dieseltravis/travis-ergogen-2024/key/output/pcbs/travis_key.kicad_pcb

## KiCad design key/output/pcbs/travis_key.kicad_pcb (2024-03-25)

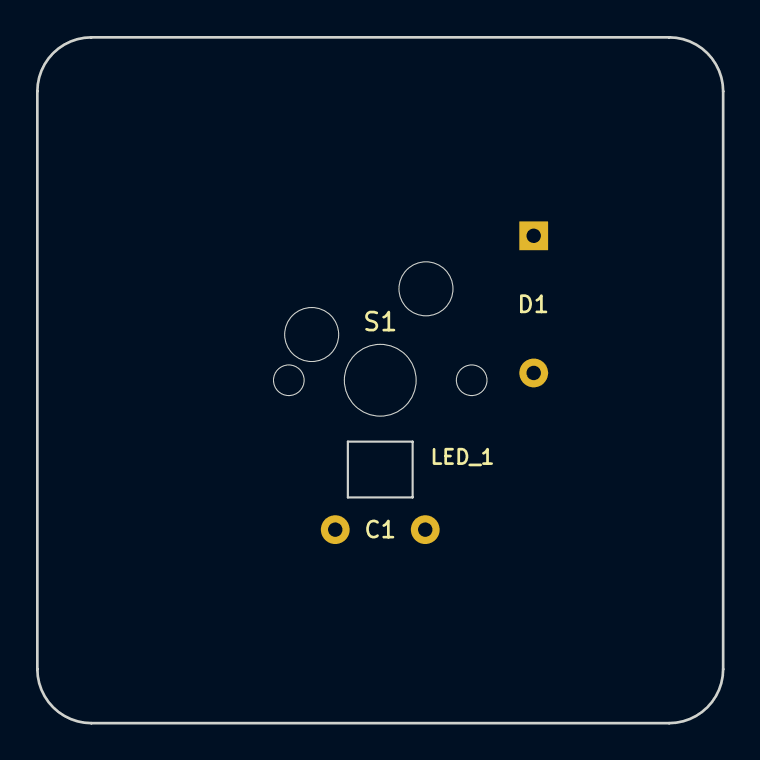
[picture p30: board travis_key.kicad_pcb from above]

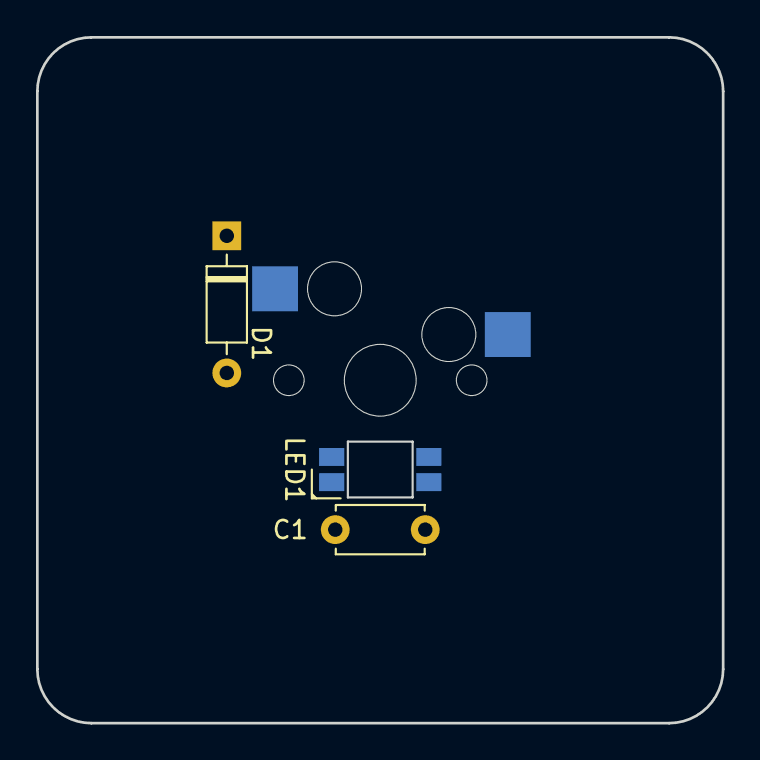
[picture p31: board travis_key.kicad_pcb from below]

Board: 2 copper layers, 38.1 x 38.1 mm, 4 parts (3 on the bottom side), 3 nets, no tracks yet.

Parts:
C1: 104; C_Disc_D4.7mm_W2.5mm_P5.00mm
D1: 1N4148; Diode_DO-35
LED1: SK6812mini-e; led_SK6812mini-e (per-key, single-side)
S1: Kailh MX Switch Sockets; MX

Connections:
GND: C1.2, LED1.3
RAW: C1.1, LED1.1
single_A_one: D1.2, S1.2
