dieseltravis/travis-ergogen-2024/keytest/output/pcbs/travis_keytest2.kicad_pcb

## KiCad design keytest/output/pcbs/travis_keytest2.kicad_pcb (2024-03-23)

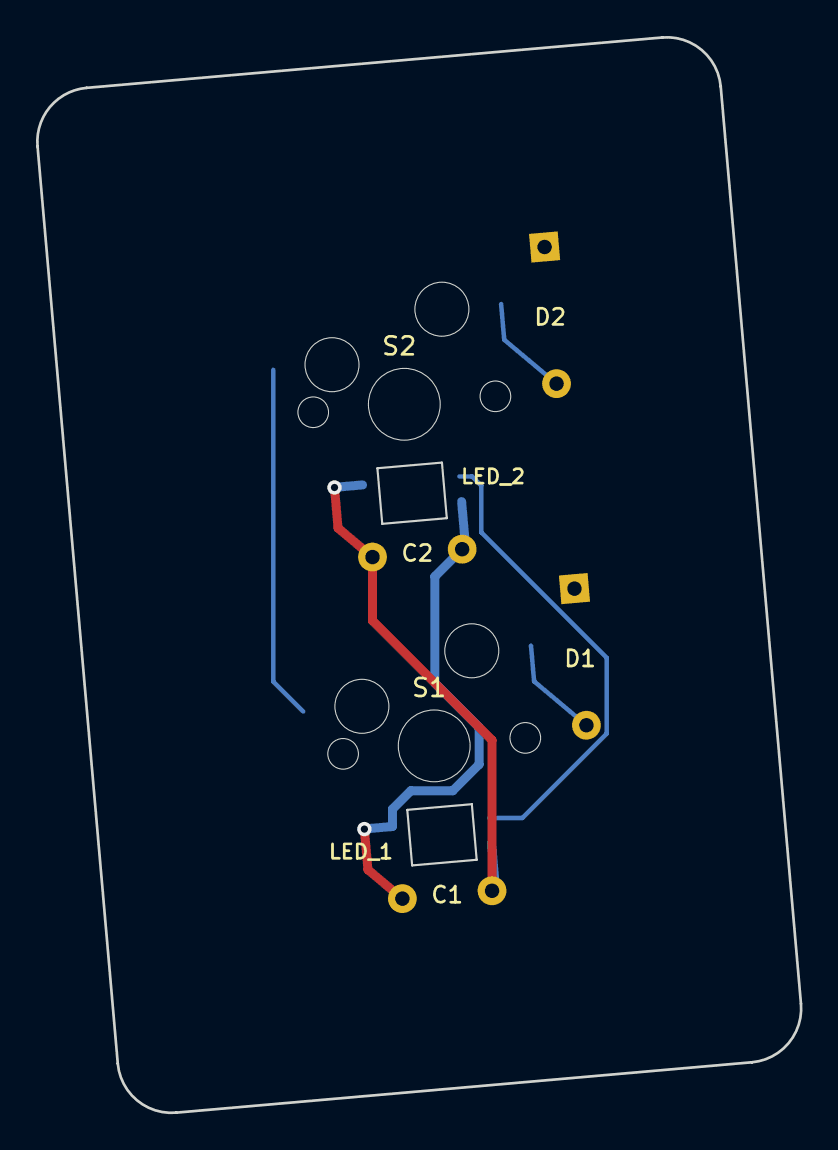
[picture p32: board travis_keytest2.kicad_pcb from above]

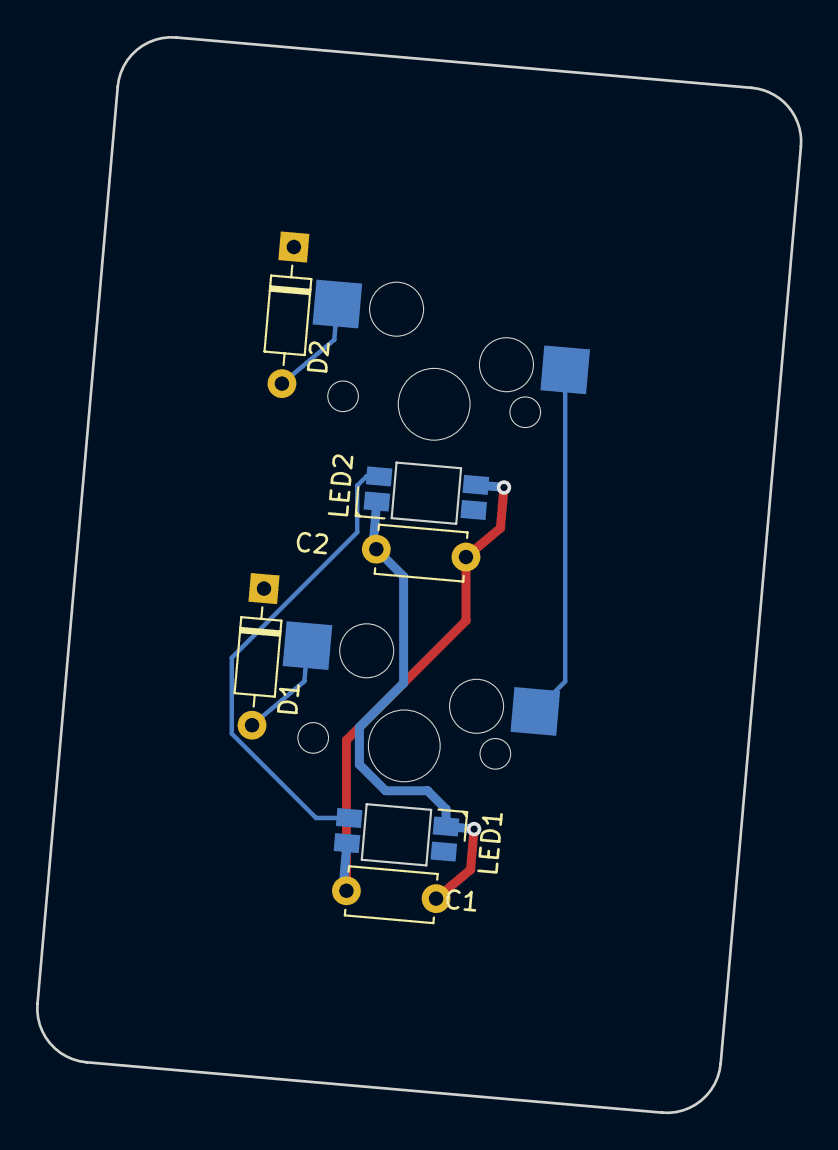
[picture p33: board travis_keytest2.kicad_pcb from below]

Board: 2 copper layers, 42.4 x 59.7 mm, 8 parts (6 on the bottom side), 6 nets.

Parts:
C1, C2: 104; C_Disc_D4.7mm_W2.5mm_P5.00mm
D1, D2: 1N4148; Diode_DO-35
LED1, LED2: SK6812mini-e; led_SK6812mini-e (per-key single-side)
S1, S2: Kailh MX Switch Sockets; MX

Connections:
GND: C1.2, C2.2, LED1.3, LED2.3
LED_2: LED1.2, LED2.4
RAW: C1.1, C2.1, LED1.1, LED2.1
col0: S1.1, S2.1
single_A_one: D1.2, S1.2
single_A_two: D2.2, S2.2
