dieseltravis/travis-ergogen-2024/output/pcbs/tutorial.kicad_pcb

## KiCad design output/pcbs/tutorial.kicad_pcb (2024-03-05)

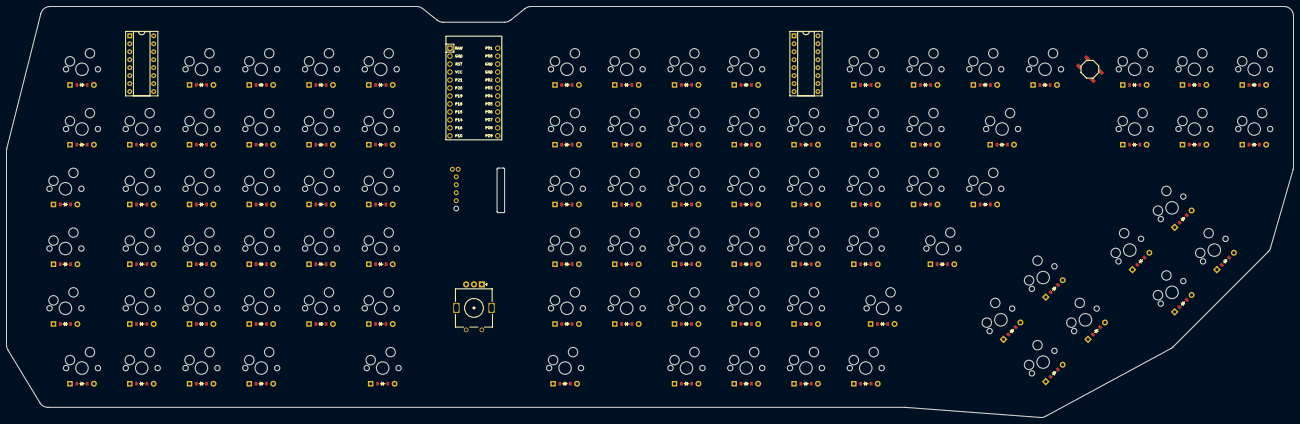
[picture p34: board tutorial.kicad_pcb from above]

Board: 2 copper layers, 410.2 x 131.0 mm, 185 parts (0 on the bottom side), 52 nets, no tracks yet.

Parts:
B1: SW_TACT_ALPS_SKQGABE010
D1, D2, D3, D4, D5, D6, D7, D8, D9, D10, D11, D12, D13, D14, D15, D16, D17, D18, D19, D20, D21, D22, D23, D24, D25, D26, D27, D28, D29, D30, D31, D32, D33, D34, D35, D36, D37, D38, D39, D40, D41, D42, D43, D44, D45, D46, D47, D48, D49, D50, D51, D52, D53, D54, D55, D56, D57, D58, D59, D60, D61, D62, D63, D64, D65, D66, D67, D68, D69, D70, D71, D72, D73, D74, D75, D76, D77, D78, D79, D80, D81, D82, D83, D84, D85, D86, D87, D88, D89, D90: ComboDiode
DIP1, DIP2: DIP-16_W7.62mm_Socket
MCU1: ProMicro
ROT1: rotary_encoder
S1, S2, S3, S4, S5, S6, S7, S8, S9, S10, S11, S12, S13, S14, S15, S16, S17, S18, S19, S20, S21, S22, S23, S24, S25, S26, S27, S28, S29, S30, S31, S32, S33, S34, S35, S36, S37, S38, S39, S40, S41, S42, S43, S44, S45, S46, S47, S48, S49, S50, S51, S52, S53, S54, S55, S56, S57, S58, S59, S60, S61, S62, S63, S64, S65, S66, S67, S68, S69, S70, S71, S72, S73, S74, S75, S76, S77, S78, S79, S80, S81, S82, S83, S84, S85, S86, S87, S88, S89, S90: MX

Connections:
GND: B1.1, DIP1.1, DIP1.2, DIP1.3, DIP1.4, DIP1.5, DIP1.6, DIP1.7, DIP1.8, DIP1.9, DIP1.10, DIP1.11, DIP1.12, DIP1.13, DIP1.14, DIP1.15, DIP2.1, DIP2.2, DIP2.3, DIP2.4, DIP2.5, DIP2.6, DIP2.7, DIP2.8, DIP2.9, DIP2.10, DIP2.11, DIP2.12, DIP2.13, DIP2.14, DIP2.15, MCU1.2, MCU1.15, MCU1.16, ROT1.1, ROT1.2, ROT1.A, ROT1.B, ROT1.C
RST: B1.2, MCU1.3
VCC: DIP1.16, DIP2.16, MCU1.4
index_bottom: D25.2, D41.2, S25.2, S41.2
index_func: D29.2, D45.2, S29.2, S45.2
index_home: D26.2, D42.2, S26.2, S42.2
index_mod: D24.2, S24.2
index_num: D28.2, D44.2, S28.2, S44.2
index_top: D27.2, D43.2, S27.2, S43.2
inner_bottom: D30.2, D36.2, S30.2, S36.2
inner_func: D34.2, D40.2, S34.2, S40.2
inner_home: D31.2, D37.2, S31.2, S37.2
inner_mod: D35.2, S35.2
inner_num: D33.2, D39.2, S33.2, S39.2
inner_top: D32.2, D38.2, S32.2, S38.2
left_bottom: D77.2, D81.2, D85.2, S77.2, S81.2, S85.2
left_top: D78.2, D82.2, D86.2, S78.2, S82.2, S86.2
mid_bottom: D87.2, S87.2
mid_top: D88.2, S88.2
middle_bottom: D19.2, D47.2, S19.2, S47.2
middle_func: D23.2, D51.2, S23.2, S51.2
middle_home: D20.2, D48.2, S20.2, S48.2
middle_mod: D18.2, D46.2, S18.2, S46.2
middle_num: D22.2, D50.2, S22.2, S50.2
middle_top: D21.2, D49.2, S21.2, S49.2
outer2_func: D72.2, S72.2
outer2_home: D69.2, S69.2
outer2_num: D71.2, S71.2
outer2_top: D70.2, S70.2
outer3_func: D75.2, S75.2
outer3_num: D74.2, S74.2
outer3_top: D73.2, S73.2
outer4_func: D76.2, S76.2
outer_bottom: D2.2, D64.2, S2.2, S64.2
outer_func: D6.2, D68.2, S6.2, S68.2
outer_home: D3.2, D65.2, S3.2, S65.2
outer_mod: D1.2, D63.2, S1.2, S63.2
outer_num: D5.2, D67.2, S5.2, S67.2
outer_top: D4.2, D66.2, S4.2, S66.2
pinky_bottom: D8.2, D59.2, S8.2, S59.2
pinky_home: D9.2, D60.2, S9.2, S60.2
pinky_mod: D7.2, D58.2, S7.2, S58.2
pinky_num: D11.2, D62.2, S11.2, S62.2
pinky_top: D10.2, D61.2, S10.2, S61.2
right_bottom: D79.2, D83.2, D89.2, S79.2, S83.2, S89.2
right_top: D80.2, D84.2, D90.2, S80.2, S84.2, S90.2
ring_bottom: D13.2, D53.2, S13.2, S53.2
ring_func: D17.2, D57.2, S17.2, S57.2
ring_home: D14.2, D54.2, S14.2, S54.2
ring_mod: D12.2, D52.2, S12.2, S52.2
ring_num: D16.2, D56.2, S16.2, S56.2
ring_top: D15.2, D55.2, S15.2, S55.2
