dieseltravis/travis-ergogen-2024/footprints/travis/ScottoKeebs-RP2040_Pro_Micro.js

// ScottoKeebs-RP2040_Pro_Micro
// https://github.com/joe-scotto/scottokeebs/blob/main/Extras/ScottoKicad/footprints/ScottoKeebs_MCU.pretty/RP2040_Pro_Micro.kicad_mod
module.exports = {
    params: {
        designator: 'MCU',
        value: 'RP2040_Pro_Micro',
        // only F for now: side: 'F',
        refpos: [0, 1.625],
        valpos: [0, 0],
        offset3d: [0, 0, 0],
        // this footprint is different from Ergogen promicro
        // pads are numbered to match Scotto footprint labelling
        // pads are mapped to promicro pin AVR names when possible
        // Left (top to bottom):           // alt pin names (GPIO/PIO/PWM, SPI, ADC, I2C, UART):
        P1:  {type: 'net', value: 'GP10'}, // GP10 SPI1SCK I2C1SDA
        P2:  {type: 'net', value: 'D3'  }, // GP0  SPI0RX  I2C0SDA UART0TX
        P3:  {type: 'net', value: 'D2'  }, // GP1  SPI0CSn I2C0SCL UART0RX
        // Unmapped: BOOT
        P4:  {type: 'net', value: 'GND' }, // ground
        P5:  {type: 'net', value: 'GND' }, // ground
        P6:  {type: 'net', value: 'D1'  }, // GP2  SPI0SCK I2C1SDA
        P7:  {type: 'net', value: 'D0'  }, // GP3  SPI0TX  I2C1SCL
        P8:  {type: 'net', value: 'D4'  }, // GP4  SPI0RX  I2C0SDA UART1TX
        P9:  {type: 'net', value: 'C6'  }, // GP5  SPI0CSn I2C0SCL UART1RX
        P10: {type: 'net', value: 'D7'  }, // GP6  SPI0SCK I2C1SDA
        P11: {type: 'net', value: 'E6'  }, // GP7  SPI0TX  I2C1SCL
        P12: {type: 'net', value: 'B4'  }, // GP8  SPI1RX  I2C1SDA
        P13: {type: 'net', value: 'B5'  }, // GP9  SPI1CSn I2C0SCL UART1TX
        // Unmapped: GPIO25, SPI0 CSn, I2C0 SDA, UART0 RX
        // Bottom Pins
        P14: {type: 'net', value: 'GP12'}, // GP12 SPI1RX  I2C0SDA UART0TX
        P15: {type: 'net', value: 'GP13'}, // GP13 SPI1CSn I2C0SCL UART0RX
        P16: {type: 'net', value: 'GP14'}, // GP14 SPI1SCK I2C1SDA
        P17: {type: 'net', value: 'GP15'}, // GP15 SPI1TX  I2C1SCL
        P18: {type: 'net', value: 'GP16'}, // GP16 SPI0RX  I2C0SDA UART0TX
        // Right (bottom to top):
        P19: {type: 'net', value: 'B6'  }, // GP21         I2C0SCL
        P20: {type: 'net', value: 'B2'  }, // GP23
        // RGB LED: GPIO17
        P21: {type: 'net', value: 'B3'  }, // GP20         I2C0SDA
        P22: {type: 'net', value: 'B1'  }, // GP22
        P23: {type: 'net', value: 'F7'  }, // GP26 ADC0    I2C1SDA
        P24: {type: 'net', value: 'F6'  }, // GP27 ADC1    I2C1SCL
        // Unmapped: GPIO18, SPI0 SCK, I2C0 SDA
        // Unmapped: GPIO24
        P25: {type: 'net', value: 'F5'  }, // GP28 ADC2
        P26: {type: 'net', value: 'F4'  }, // GP29 ADC3
        P27: {type: 'net', value: 'VCC' }, // 3V3
        P28: {type: 'net', value: 'RST' }, // reset
        P29: {type: 'net', value: 'GND' }, // ground
        P30: {type: 'net', value: 'RAW' }, // 5V
        P31: {type: 'net', value: 'GP11'}, // GP11 SPI1TX  I2C1SCL
        SCOTTOKEEBS_KICAD: '${SCOTTOKEEBS_KICAD}'
    },
    body: p => {
        const pos = (arr) => arr.join(' ');
        if (p.refpos.length === 2) {
          p.refpos.push(p.r);
        }
        if (p.valpos.length === 2) {
          p.valpos.push(p.r);
        }
        const lblrot = (rot) => {
            // rotate and adjust rotation for readability
            if (rot > 90 || rot < -90) {
                rot += 180;
            }
            return rot;
        };
        const lbljust = (rot, justify) => {
            // rotate and adjust justify left/right for readability
            if (rot > 90 || rot < -90) {
                if (justify === 'left') {
                    justify = 'right';
                } else if (justify === 'right') {
                    justify = 'left';
                }
                // ignore center
            }
            return justify;
        };
        return `(footprint "RP2040_Pro_Micro"
	(version 20240108)
	(generator "pcbnew")
	(generator_version "8.0")
	(layer "F.Cu")
    ${p.at /* parametric position */}

	(property "Reference" "${p.ref}"
		(at ${pos(p.refpos)})
		(layer "F.SilkS")
		(hide yes)
		(uuid "424c16a4-34f7-4430-8bc4-7c0f957bed29")
		(effects
			(font
				(size 1.27 1.524)
				(thickness 0.2032)
			)
		)
	)
	(property "Value" "${p.value}"
		(at ${pos(p.valpos)})
		(layer "F.SilkS")
		(hide yes)
		(uuid "71df3eaa-4617-4573-8f7c-b46dfaa34385")
		(effects
			(font
				(size 1.27 1.524)
				(thickness 0.2032)
			)
		)
	)
	(property "Footprint" ""
		(at 0 0 0)
		(unlocked yes)
		(layer "F.Fab")
		(hide yes)
		(uuid "cca82f72-4fa7-4dbc-bf7c-0ec96f13cb3b")
		(effects
			(font
				(size 1.27 1.27)
			)
		)
	)
	(property "Datasheet" ""
		(at 0 0 0)
		(unlocked yes)
		(layer "F.Fab")
		(hide yes)
		(uuid "7b756f98-1088-4c14-b3e7-da53581f1ac4")
		(effects
			(font
				(size 1.27 1.27)
			)
		)
	)
	(property "Description" ""
		(at 0 0 0)
		(unlocked yes)
		(layer "F.Fab")
		(hide yes)
		(uuid "8a074bf2-0215-4e4c-b4a4-f20a9d9c5568")
		(effects
			(font
				(size 1.27 1.27)
			)
		)
	)
	(attr through_hole)
    (fp_text reference "${p.ref}" (at ${pos(p.refpos)}) (layer "F.SilkS") ${p.ref_hide}
        (effects (font (size 1 1) (thickness 0.15)))
    )
    (fp_text value "${p.value}" (at ${pos(p.valpos)}) (layer "F.Fab") hide
        (effects (font (size 0.8 0.8) (thickness 0.15)))
    )

	(fp_line
		(start -8.89 -17.78)
		(end -8.89 15.24)
		(stroke
			(width 0.2)
			(type solid)
		)
		(layer "B.SilkS")
		(uuid "19020500-6d69-4534-b637-d9f7fdbe90ef")
	)
	(fp_line
		(start -8.89 15.24)
		(end 8.89 15.24)
		(stroke
			(width 0.2)
			(type solid)
		)
		(layer "B.SilkS")
		(uuid "b223a3c0-4619-4cce-abc4-3ca0b5d8d929")
	)
	(fp_line
		(start 8.89 -17.78)
		(end -8.89 -17.78)
		(stroke
			(width 0.2)
			(type solid)
		)
		(layer "B.SilkS")
		(uuid "07a27397-c677-4ed6-8df4-02f6cfc97eb5")
	)
	(fp_line
		(start 8.89 15.24)
		(end 8.89 -17.78)
		(stroke
			(width 0.2)
			(type solid)
		)
		(layer "B.SilkS")
		(uuid "37aebfa3-8f8f-4c0c-8491-8c221cdc60bd")
	)
	(fp_line
		(start -8.89 -17.78)
		(end -8.89 15.24)
		(stroke
			(width 0.2)
			(type solid)
		)
		(layer "F.SilkS")
		(uuid "f1d9fc6e-b3d4-4b28-b5f5-622cf3715cd6")
	)
	(fp_line
		(start -8.89 15.24)
		(end 8.89 15.24)
		(stroke
			(width 0.2)
			(type solid)
		)
		(layer "F.SilkS")
		(uuid "864387a7-6b5e-492c-821b-a5610246d71c")
	)
	(fp_line
		(start 8.89 -17.78)
		(end -8.89 -17.78)
		(stroke
			(width 0.2)
			(type solid)
		)
		(layer "F.SilkS")
		(uuid "8fb5f32e-160c-43e6-9cab-e4f9235e7ad0")
	)
	(fp_line
		(start 8.89 15.24)
		(end 8.89 -17.78)
		(stroke
			(width 0.2)
			(type solid)
		)
		(layer "F.SilkS")
		(uuid "46ddcabf-ebe4-44b2-9de4-ae20d2cdd0ce")
	)
	(fp_line
		(start -4.5 -18.58)
		(end -4.5 -12.08)
		(stroke
			(width 0.2)
			(type default)
		)
		(layer "Dwgs.User")
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
		(remove_unused_layers no)
		(uuid "ba5c5548-69cb-4d1b-9c7e-1a283364fad4")
	)
	(model "${p.SCOTTOKEEBS_KICAD}/3dmodels/ScottoKeebs_MCU.3dshapes/RP2040_Pro_Micro.step"
		(offset
			(xyz ${pos(p.offset3d)})
		)
		(scale
			(xyz 1 1 1)
		)
		(rotate
			(xyz 0 0 0)
		)
	)
)`;
    }
};
