dieseltravis/travis-ergogen-2024/firmware/qmk/travisergogen2024.c

/* Copyright 2021 Jay Greco
 * Copyright 2022 mohoyt
 *
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
 * You should have received a copy of the GNU General Public License
 * along with this program.  If not, see <http://www.gnu.org/licenses/>.
 */
#include QMK_KEYBOARD_H
#include "travisergogen2024.h"
